L0r3nz0000/Robot-arm/3D_models/MK2 Plus/EBAmk2_004_link135.STL

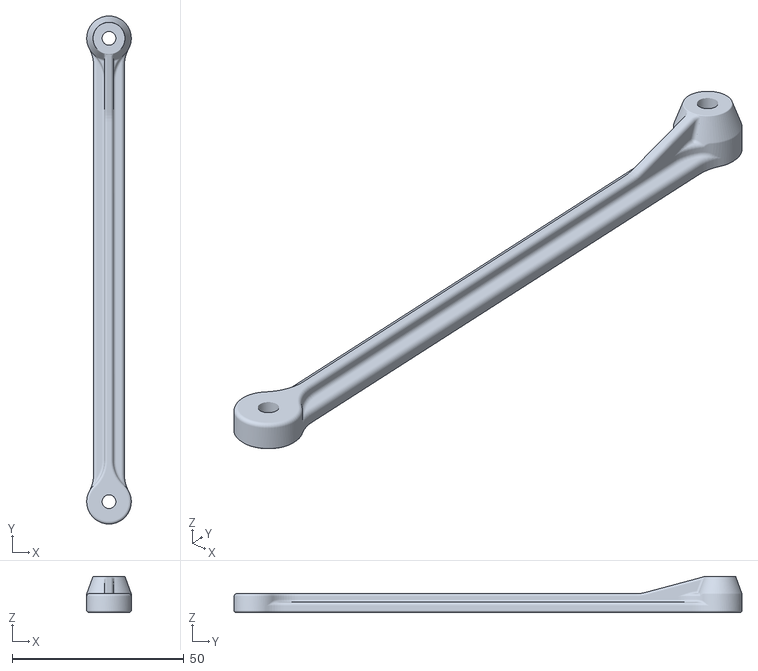
[picture p21: CAD file, 2025-03-28]
3D_models/MK2 Plus/EBAmk2_004_link135.STL
13.0 x 148.0 x 10.5
