L0r3nz0000/Robot-arm/3D_models/MK2 Plus/Base_Bearing_Ball.STL

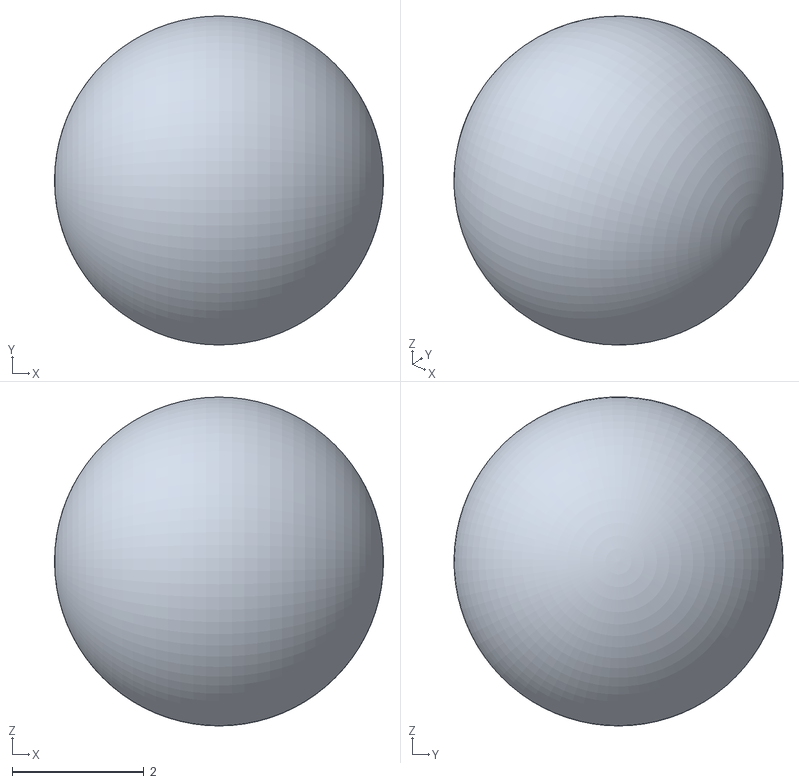
[picture p22: CAD file, 2025-03-28]
3D_models/MK2 Plus/Base_Bearing_Ball.STL
5.00 x 5.00 x 5.00
