L0r3nz0000/Robot-arm/3D_models/MK2 Plus/Robot_Base_Low.STL

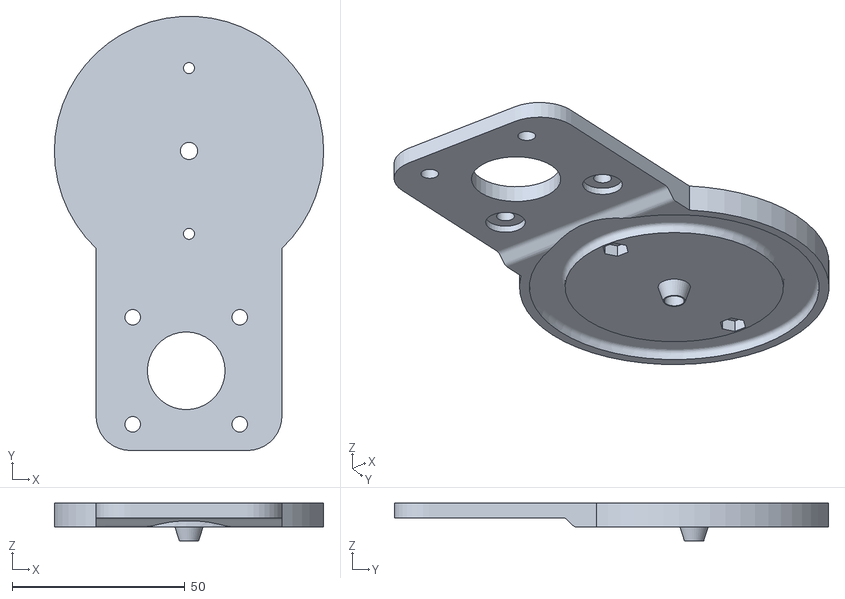
[picture p23: CAD file, 2025-03-28]
3D_models/MK2 Plus/Robot_Base_Low.STL
78.0 x 125.7 x 11.0
