L0r3nz0000/Robot-arm/3D_models/MK2 Plus/EBAmk2_006_horarm__.STL

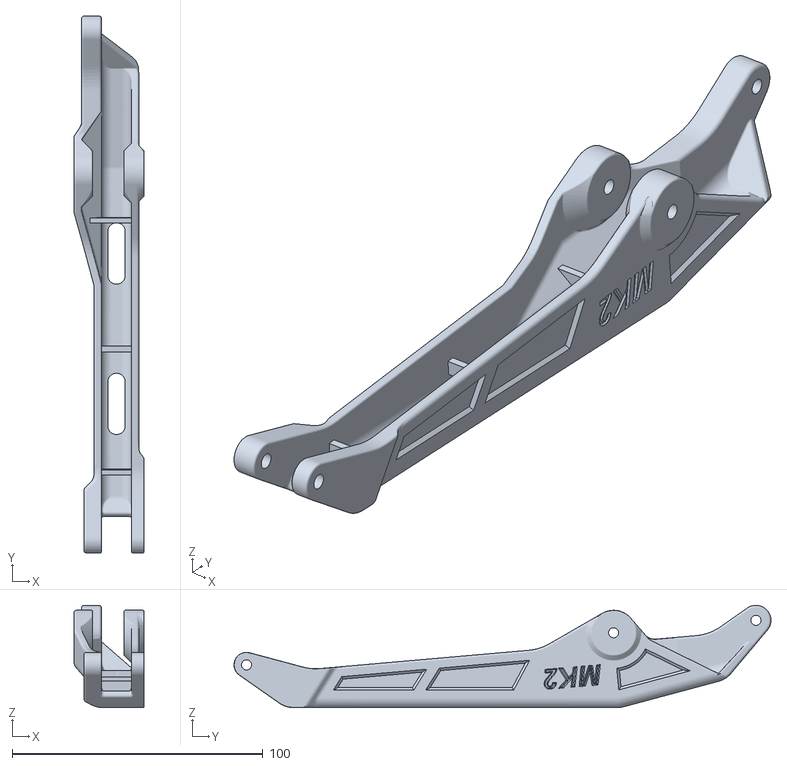
[picture p24: CAD file, 2025-03-28]
3D_models/MK2 Plus/EBAmk2_006_horarm__.STL
28.0 x 214.2 x 40.9
