L0r3nz0000/Robot-arm/3D_models/MK2 Plus/EBAmk2_005_link135angled.STL

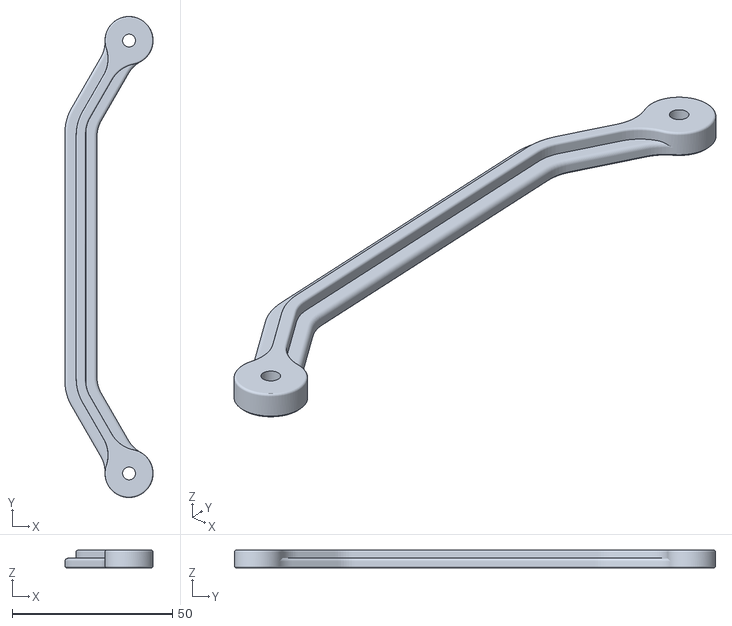
[picture p25: CAD file, 2025-03-28]
3D_models/MK2 Plus/EBAmk2_005_link135angled.STL
27.5 x 150.0 x 5.50
