L0r3nz0000/Robot-arm/3D_models/MK2 Plus/finalholder.STL

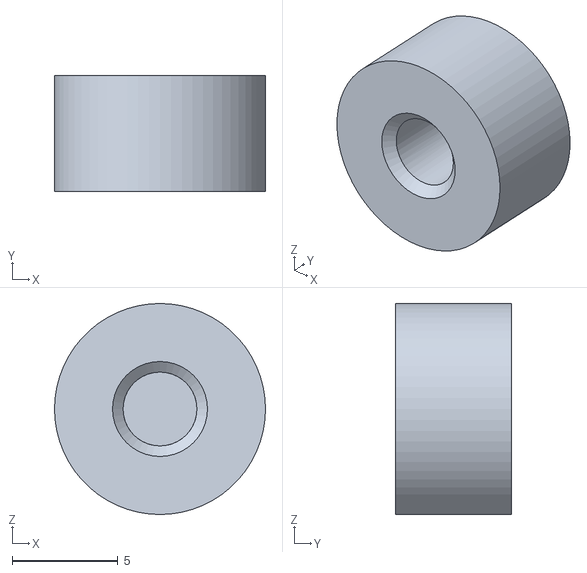
[picture p26: CAD file, 2025-03-28]
3D_models/MK2 Plus/finalholder.STL
10.0 x 5.50 x 10.0
