L0r3nz0000/Robot-arm/3D_models/MK2 Plus/Robot_Base_Low_Gear.STL

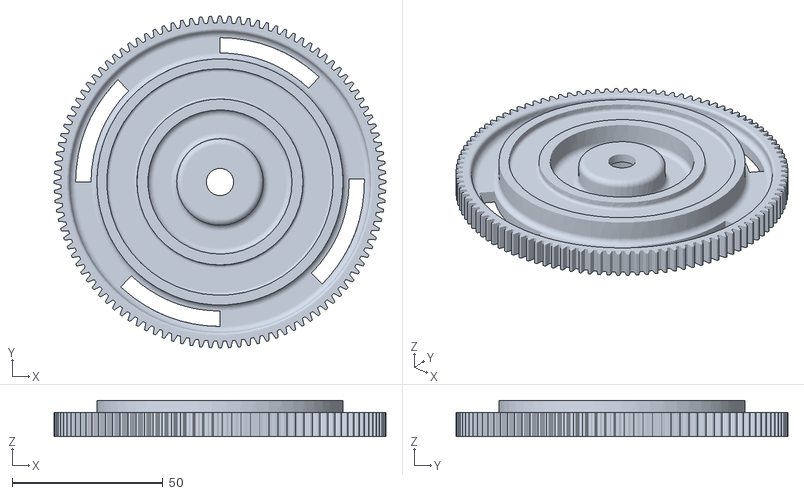
[picture p27: CAD file, 2025-03-28]
3D_models/MK2 Plus/Robot_Base_Low_Gear.STL
110.0 x 110.0 x 12.0
