L0r3nz0000/Robot-arm/3D_models/MK2 Plus/Base_Arm.STL

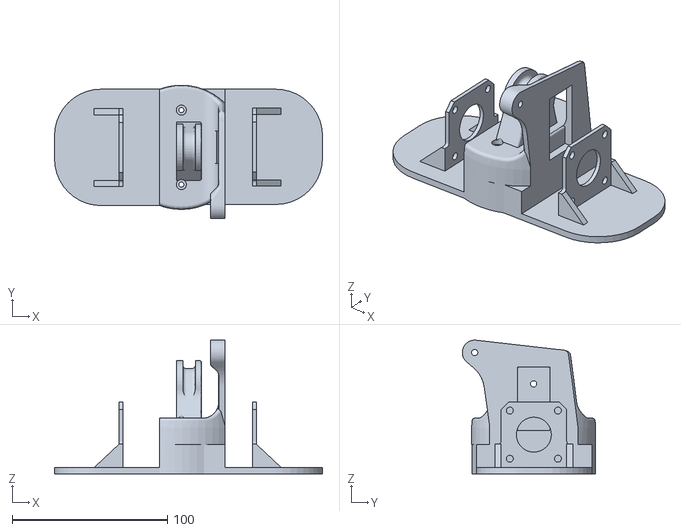
[picture p28: CAD file, 2025-03-28]
3D_models/MK2 Plus/Base_Arm.STL
172.7 x 86.0 x 86.2
