L0r3nz0000/Robot-arm/3D_models/MK2 Plus/EBAmk2_009_trialinkfront.STL

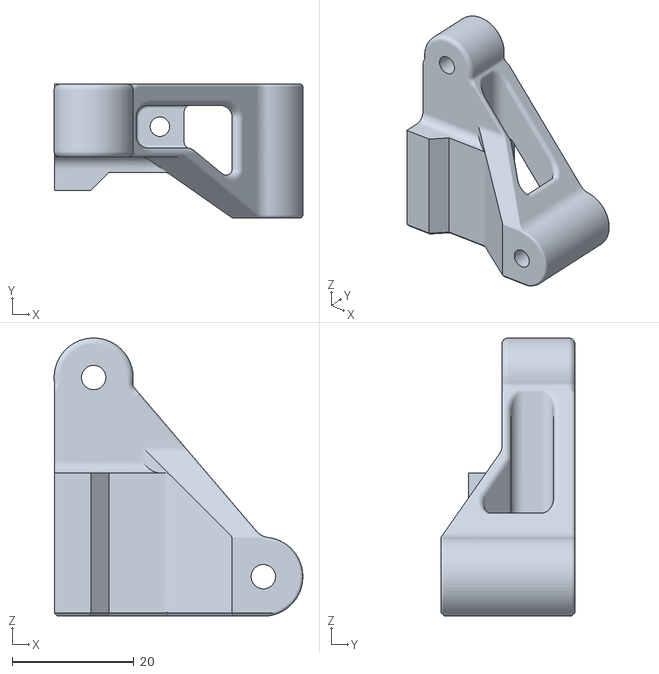
[picture p29: CAD file, 2025-03-28]
3D_models/MK2 Plus/EBAmk2_009_trialinkfront.STL
40.9 x 22.0 x 45.7
